makingdevices/PicBytesMicro/Simulation&Firmware/Source & simulations/graphics.h

/*	Making Devices 2024
	https://makingdevices.com
	Rubén García Segovia
	Pic Bytes Micro
*/
#ifndef __graphics
#define __graphics

#pragma idata my_memory_section_1
char letter_number[10][5] = {
	{ // NR 0
	 0b01100000,
     0b10010000,
	 0b10010000,
	 0b10010000,
	 0b01100000,
	},
	{ // NR 1
	 0b01100000,
     0b00100000,
	 0b00100000,
	 0b00100000,
	 0b01110000,
	},
	{ // NR 2
	 0b11100000,
     0b00010000,
	 0b00100000,
	 0b01000000,
	 0b11110000,
	},
	{ // NR 3
	 0b11100000,
     0b00010000,
	 0b11100000,
	 0b00010000,
	 0b11100000,
	},
	{ // NR 4
	 0b10010000,
     0b10010000,
	 0b11110000,
	 0b00010000,
	 0b00010000,
	},
	{ // NR 5
	 0b11110000,
     0b10000000,
	 0b111100000,
	 0b00010000,
	 0b11100000,
	},
	{ // NR 6
	 0b11110000,
     0b10000000,
	 0b11110000,
	 0b10010000,
	 0b11110000,
	},
	{ // NR 7
	 0b11110000,
     0b00010000,
	 0b00100000,
	 0b01000000,
	 0b10000000,
	},
	{ // NR 8
	 0b11110000,
     0b10010000,
	 0b01100000,
	 0b10010000,
	 0b11110000,
	},
	{ // NR 9
	 0b01100000,
     0b10010000,
	 0b01100000,
	 0b00010000,
	 0b00010000,
	}
};
#pragma idata

char letter_blank[5] = { 
	 0b00000000,
     0b00000000,
	 0b00000000,
	 0b00000000,
	 0b00000000,
};

char letter_A[5] = { 
	 0b01100000,
     0b10010000,
	 0b11110000,
	 0b10010000,
	 0b10010000,
};

char letter_A_small[5] = { 
	 0b01000000,
     0b10100000,
	 0b11100000,
	 0b10100000,
	 0b10100000,
};

char letter_B[5] = { 
	 0b11100000,
     0b10100000,
	 0b11100000,
	 0b10100000,
	 0b11100000,
};


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
	 0b11110000,
     0b10010000,
	 0b11010000,
	 0b00000000,
	 0b00010000,
};

char letter_tick[5] = { 
	 0b00000000,
     0b00010000,
	 0b10100000,
	 0b01000000,
	 0b00000000,
};

char letter_cross[5] = { 
	 0b10010000,
     0b01100000,
	 0b01100000,
	 0b10010000,
	 0b00000000,
};

#endif
